Patsch91/NerdOCTAXE-Gamma/Images/20250406_103209.jpg

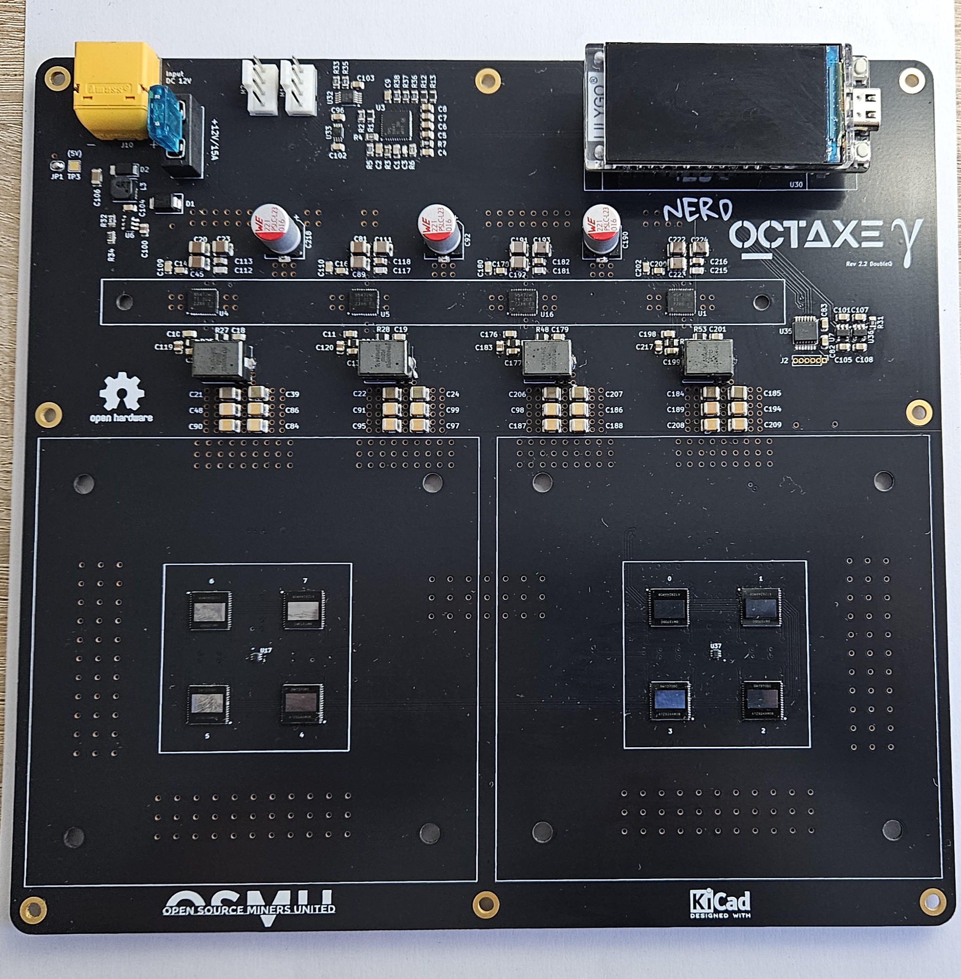
Images/20250406_103209.jpg
