Patsch91/NerdOCTAXE-Gamma/Images/20250408_185311.jpg

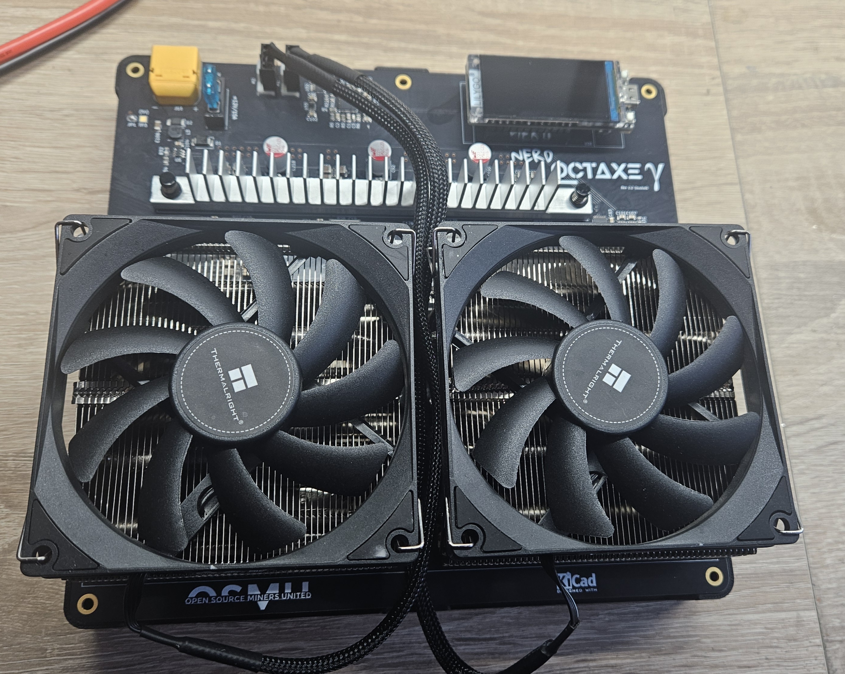
Images/20250408_185311.jpg
